jarodcsaxberg/light-monitoring-system/enclosure/Base/e314 base v4.png

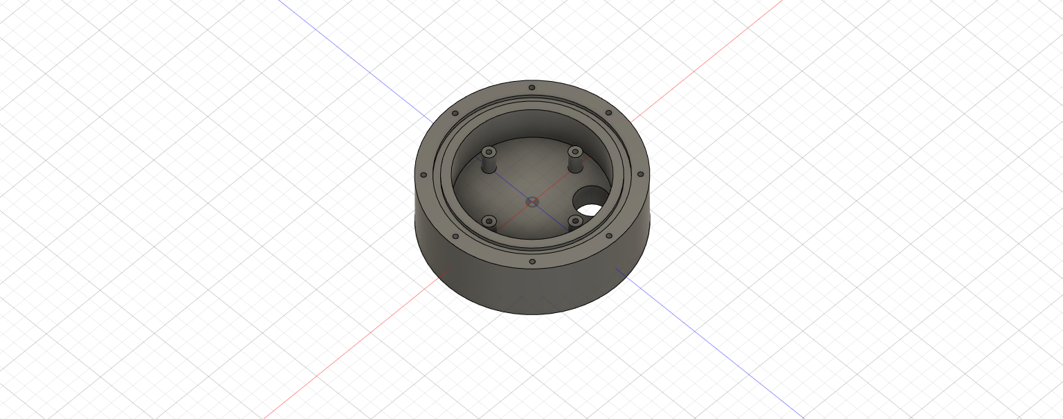
enclosure/Base/e314 base v4.png
