jarodcsaxberg/light-monitoring-system/enclosure/Lid/e314 lid v1.png

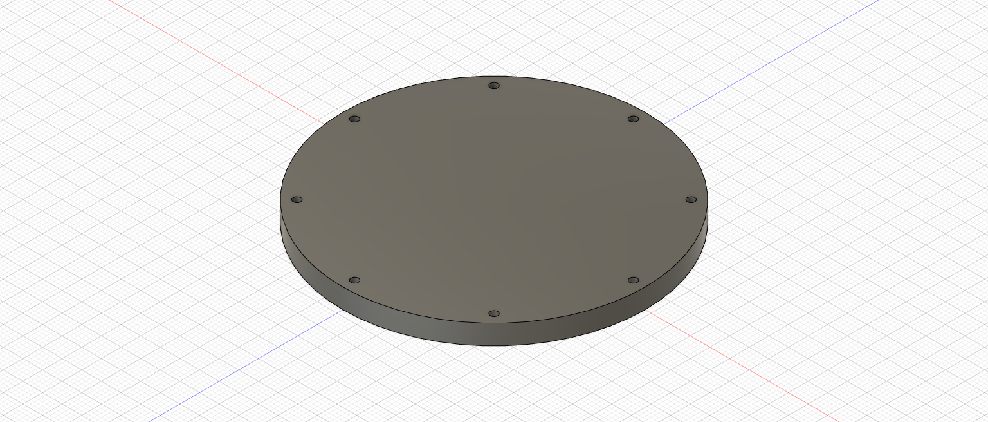
enclosure/Lid/e314 lid v1.png
