jarodcsaxberg/light-monitoring-system/kicad_proj/Osh Park Screenshot.jpg

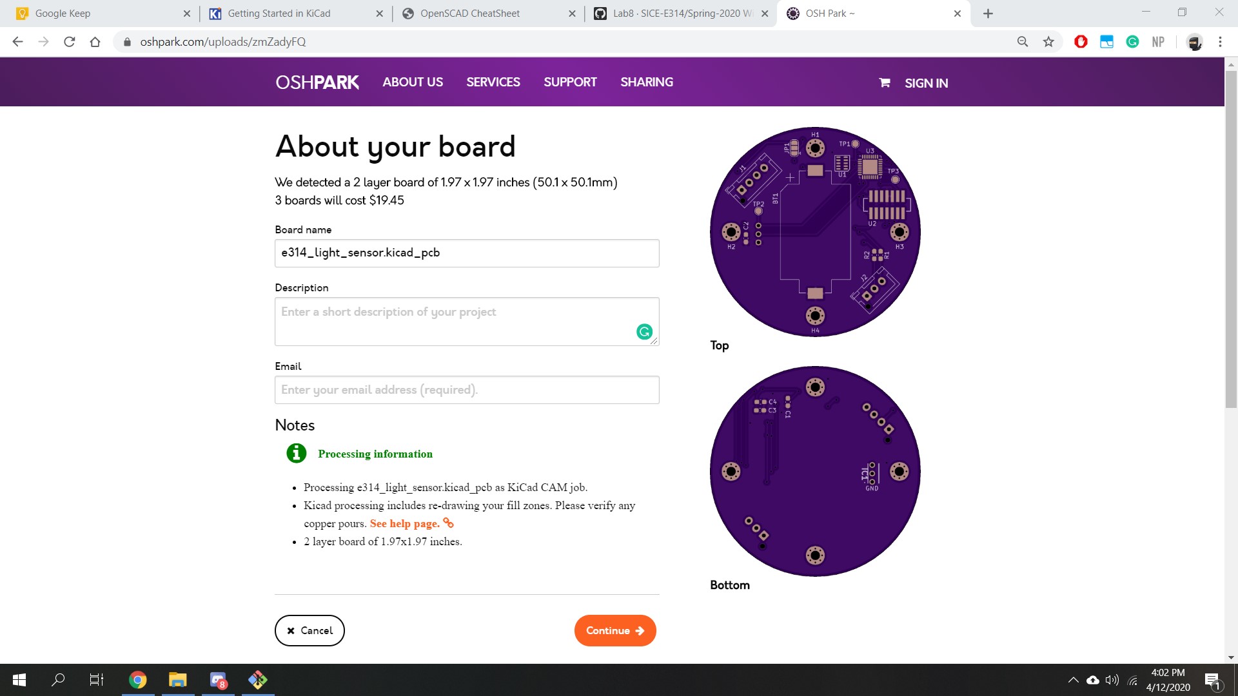
kicad_proj/Osh Park Screenshot.jpg
