jarodcsaxberg/light-monitoring-system/project/Inc/log.h

#ifndef _LOG_H__
#define _LOG_H__

#define SENSOR_DATA 0x01
#define LOG_DATA 0x02
#define FLASH_END          0x0803FFF0

#define SENTINEL_MARK_BOTTOM   0xDEADBEEFA5A5A5A5
#define SENTINEL_MARK_TOP      0xFEEDC0DE5A5A5A5A

#define MASK_WATERMARK         0x00000000000000FF
#define MASK_STATUS            0x000000000000FF00
#define MASK_RECORD_NUMBER     0x00000000FFFF0000
#define MASK_TIMESTAMP         0xFFFFFFFF00000000

#define MASK_VOLTAGE           0x000000000000FFFF
#define MASK_TEMPERATURE       0x00000000FFFF0000
#define MASK_SENSOR_PERIOD     0xFFFFFFFF00000000

typedef struct sensordata {
  uint8_t watermark;               // 0x01=populated, 0xFF=unpopulated
  uint8_t status;                  // record type, 01=sensor data, 02=log data;
  uint16_t record_number;          // Which number is this particular record
  uint32_t timestamp;              // Time, bit packed into 32 bits
  uint16_t battery_voltage;        // 16 bit battery voltage
  int16_t temperature;             // STM32 Temperature sensor reading
  uint32_t sensor_period;          // Reading from the light sensor
} sensordata_t;

typedef struct logdata {
  uint8_t watermark;               // 0x01=populated, 0xFF=unpopulated
  uint8_t status;                  // record type, 01=sensor data, 02=log data;
  uint16_t record_number;          // Which number is this particular record
  uint32_t timestamp;              // Time, bit packed into 32 bits
  uint8_t msg[8];                  // String message to make the record seem less cryptic.
} logdata_t;

typedef struct raw {               // Raw structure used to write sensordata and log_data to the flash
  uint64_t data0;
  uint64_t data1;
} raw_t;

typedef struct flash_status {
  uint64_t* data_start;
  uint32_t total_records; //possibly unnecessary? same as next_record_number
  uint32_t max_possible_records;
  uint64_t* next_address;
  uint32_t next_record_number;
} flash_status_t;

void print_logs(int);
void print_data(int);

uint8_t store_entry(void);
uint8_t log_entry(char *);

uint8_t flash_write_init(/*flash_status_t *  */);
uint8_t write_record(/*flash_status_t *, */void *);
int flash_erase(void);

/*uint64_t *find_sentinel_top(uint64_t *, uint64_t *);    //no longer used*/
uint64_t *find_sentinel_bottom(uint64_t *, uint64_t *);

uint8_t write_sentinel(uint64_t *, raw_t *);
int flash_erase(void);
static uint32_t GetPage(uint32_t);
static uint32_t GetBank(uint32_t);
#endif
